GPTmadeit/juggernaut-molle-pixel-cases/pixel-6a/preview/S_case_back.png

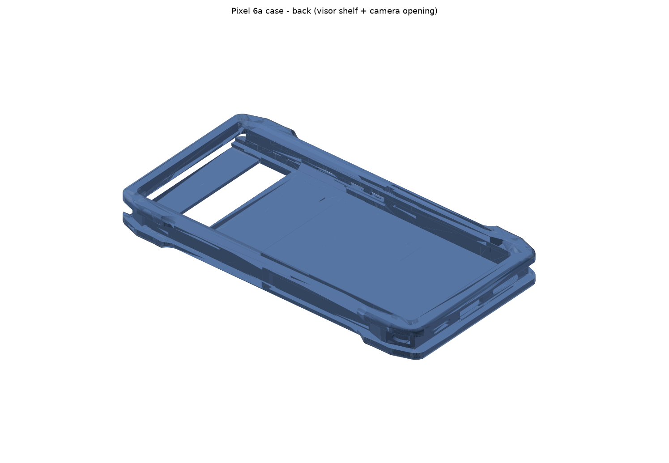
pixel-6a/preview/S_case_back.png
