GPTmadeit/juggernaut-molle-pixel-cases/pixel-6a/preview/S_case_mount.png

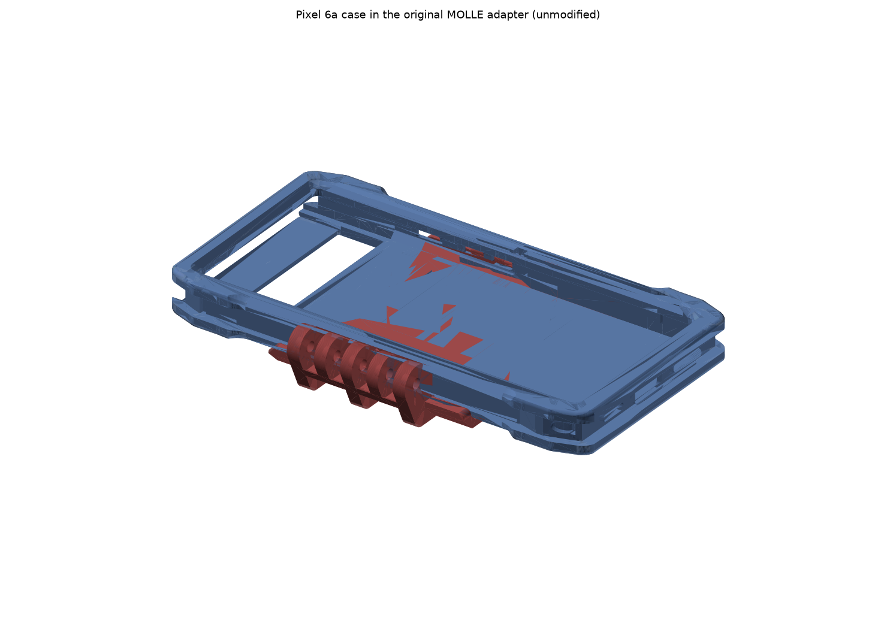
pixel-6a/preview/S_case_mount.png
