GPTmadeit/juggernaut-molle-pixel-cases/pixel-9-pro/preview/N_case_phone.png

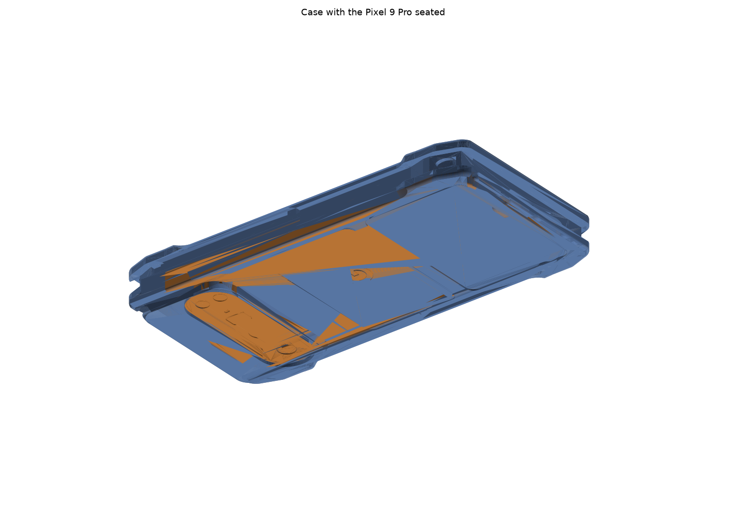
pixel-9-pro/preview/N_case_phone.png
