GPTmadeit/juggernaut-molle-pixel-cases/pixel-9-pro/top_cap_pixel9pro.stl

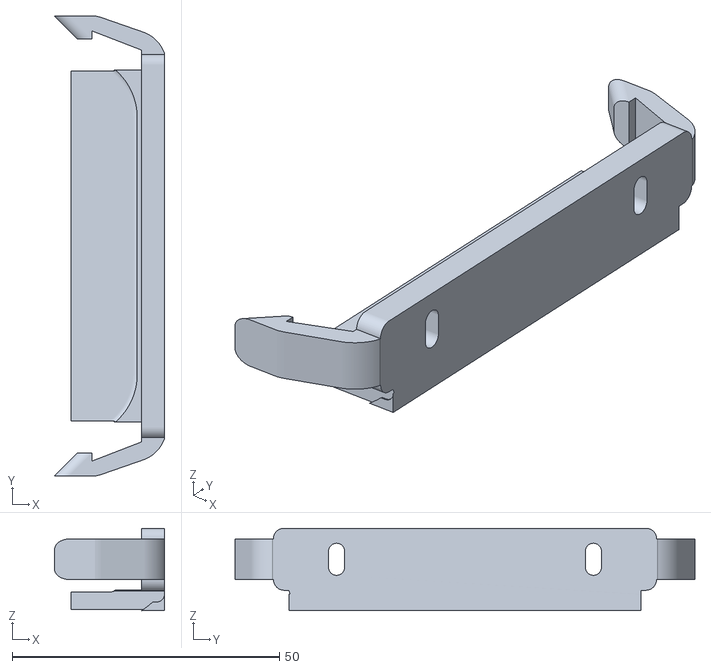
[picture p25: CAD file, 2026-09-12]
pixel-9-pro/top_cap_pixel9pro.stl
20.6 x 86.0 x 15.4
