GPTmadeit/juggernaut-molle-pixel-cases/pixel-9a/volume_button_pixel9a.stl

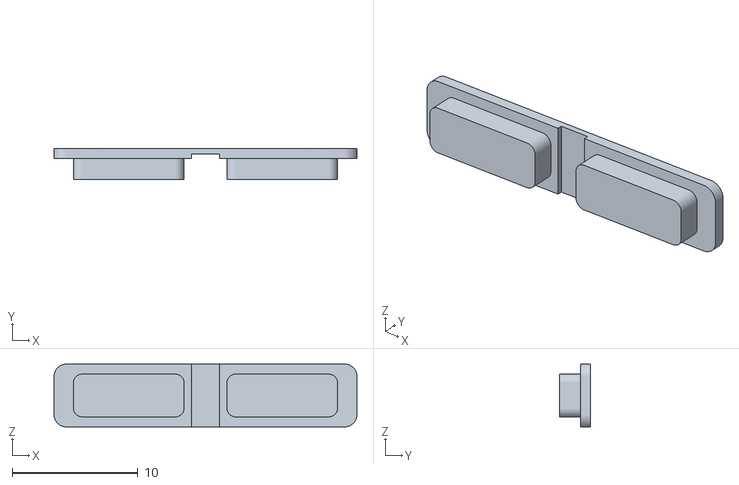
[picture p26: CAD file, 2026-09-11]
pixel-9a/volume_button_pixel9a.stl
24.1 x 2.48 x 5.00
