GPTmadeit/juggernaut-molle-pixel-cases/pixel-6a/case_pixel6a.stl

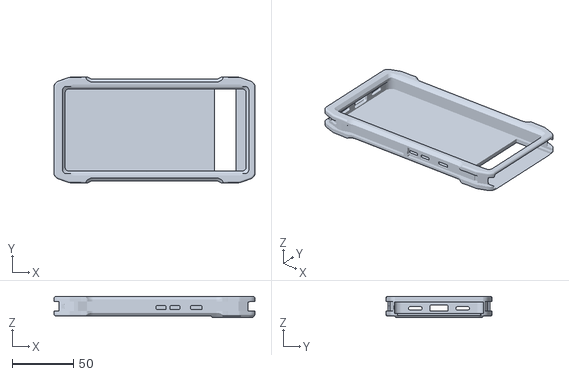
[picture p27: CAD file, 2026-09-11]
pixel-6a/case_pixel6a.stl
163.8 x 86.6 x 17.2
