GPTmadeit/juggernaut-molle-pixel-cases/pixel-9-pro/power_button_pixel9pro.stl

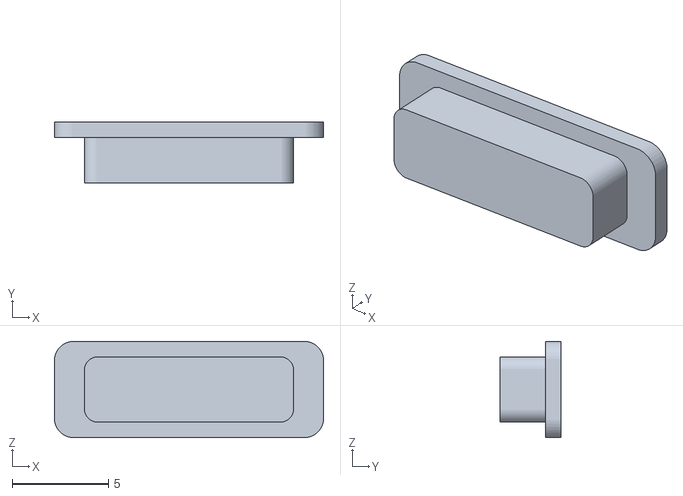
[picture p28: CAD file, 2026-09-12]
pixel-9-pro/power_button_pixel9pro.stl
14.0 x 3.18 x 4.98
