GPTmadeit/juggernaut-molle-pixel-cases/pixel-9a/power_button_pixel9a.stl

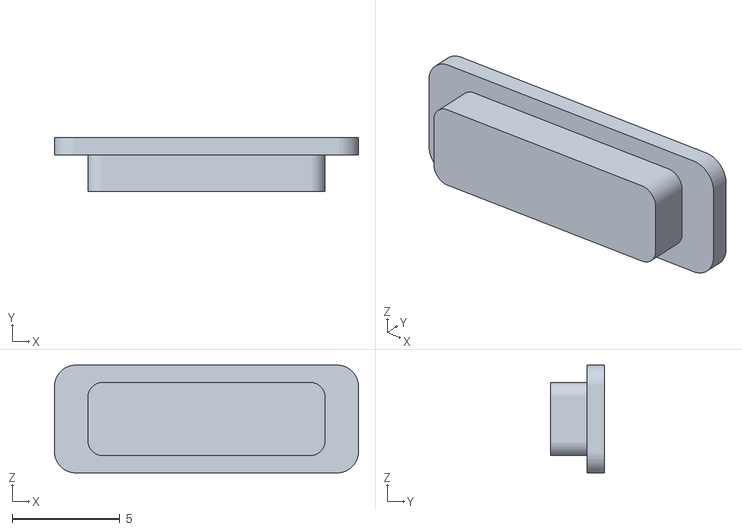
[picture p29: CAD file, 2026-09-11]
pixel-9a/power_button_pixel9a.stl
14.1 x 2.48 x 4.99
