GPTmadeit/juggernaut-molle-pixel-cases/pixel-6a/volume_button_pixel6a.stl

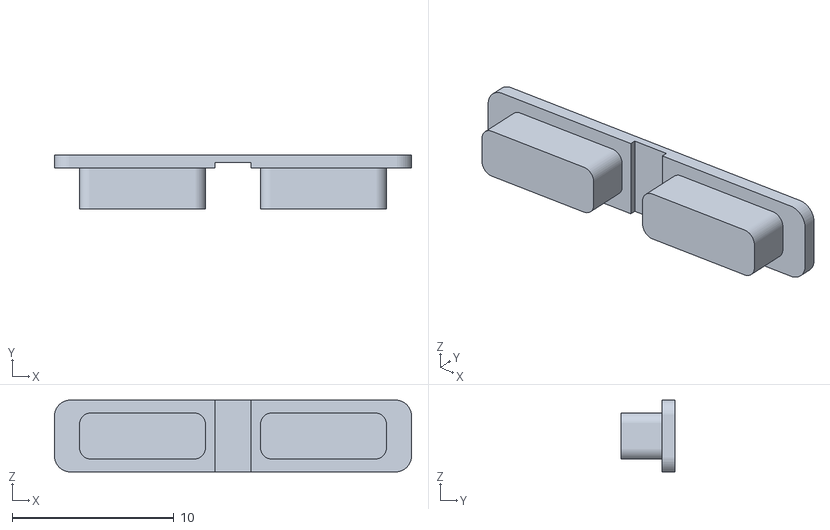
[picture p30: CAD file, 2026-09-11]
pixel-6a/volume_button_pixel6a.stl
22.1 x 3.34 x 4.45
