GPTmadeit/juggernaut-molle-pixel-cases/pixel-9-pro/case_pixel9pro.stl

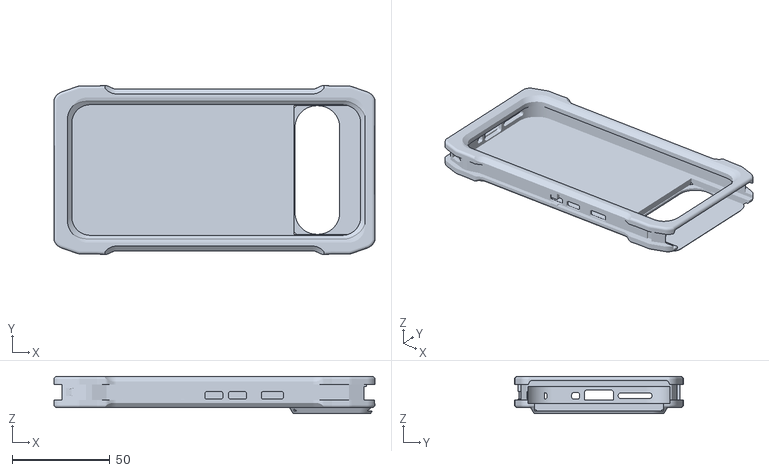
[picture p31: CAD file, 2026-09-12]
pixel-9-pro/case_pixel9pro.stl
164.4 x 86.6 x 19.0
