GPTmadeit/juggernaut-molle-pixel-cases/pixel-9a/case_pixel9a.stl

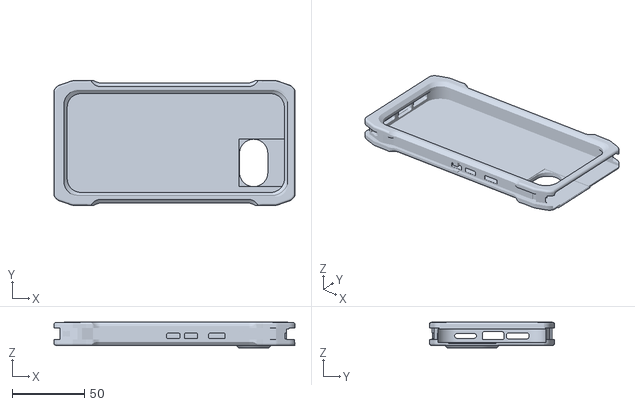
[picture p32: CAD file, 2026-09-11]
pixel-9a/case_pixel9a.stl
166.3 x 86.6 x 17.6
