GPTmadeit/juggernaut-molle-pixel-cases/pixel-6a/power_button_pixel6a.stl

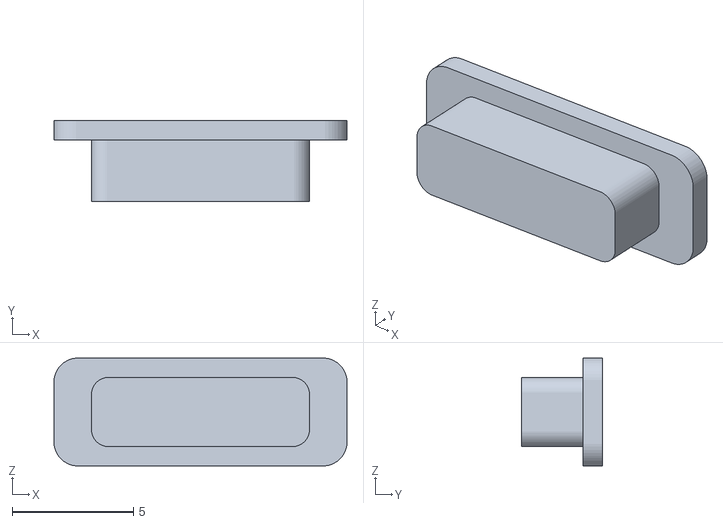
[picture p33: CAD file, 2026-09-11]
pixel-6a/power_button_pixel6a.stl
12.1 x 3.34 x 4.44
