GPTmadeit/juggernaut-molle-pixel-cases/pixel-9-pro/volume_button_pixel9pro.stl

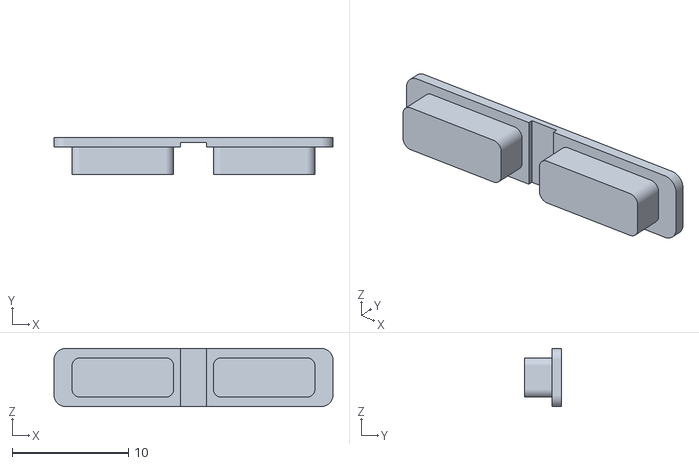
[picture p34: CAD file, 2026-09-12]
pixel-9-pro/volume_button_pixel9pro.stl
24.0 x 3.18 x 4.99
