GPTmadeit/juggernaut-molle-pixel-cases/pixel-9a/camera_protector_cap_pixel9a.stl

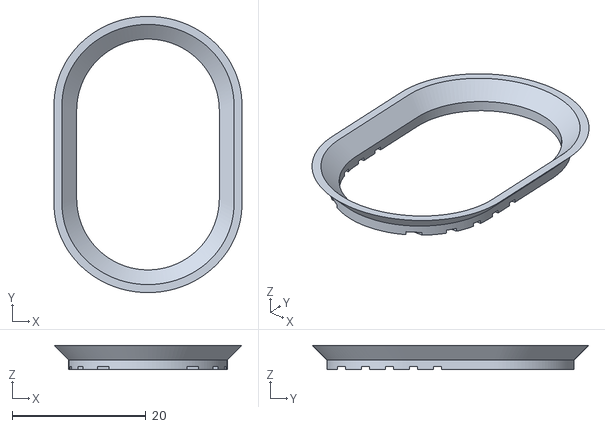
[picture p35: CAD file, 2026-09-11]
pixel-9a/camera_protector_cap_pixel9a.stl
28.1 x 41.3 x 3.60
