GPTmadeit/juggernaut-molle-pixel-cases/pixel-6a/preview/S_assembly.png

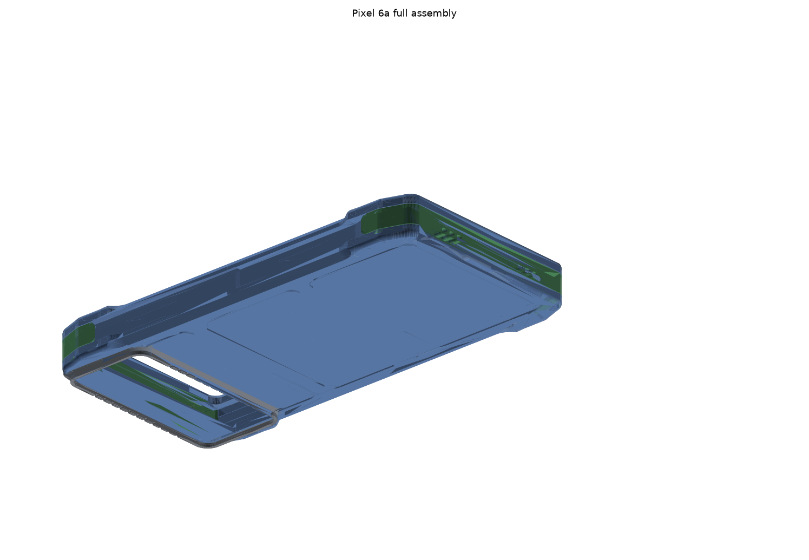
pixel-6a/preview/S_assembly.png
