GPTmadeit/juggernaut-molle-pixel-cases/pixel-9-pro/preview/N_assembly.png

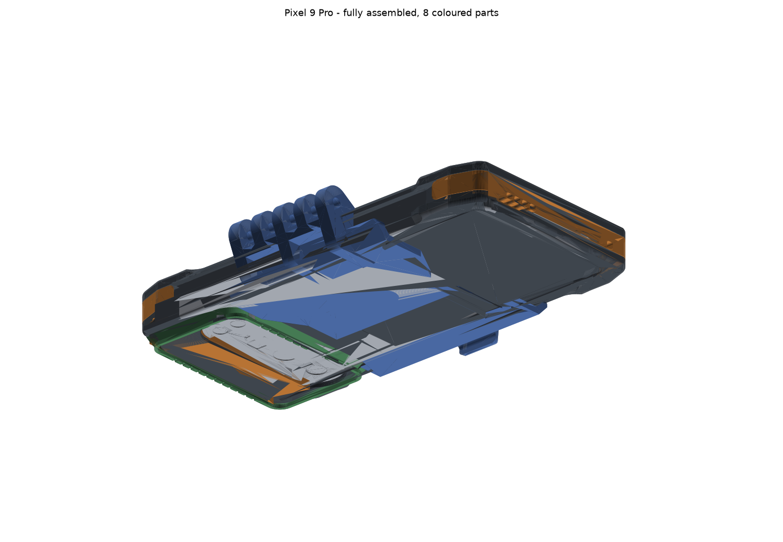
pixel-9-pro/preview/N_assembly.png
