GPTmadeit/juggernaut-molle-pixel-cases/pixel-9a/preview/F_assembly.png

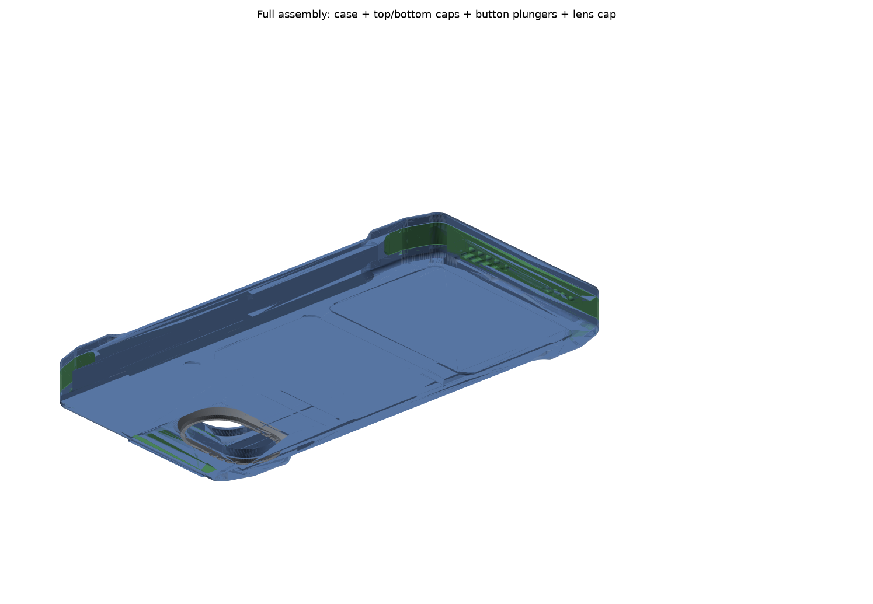
pixel-9a/preview/F_assembly.png
